XIAOYUsamaQAQ123/senior-design-notebook/notebook/Liangcheng Sun/final_presentation.pdf

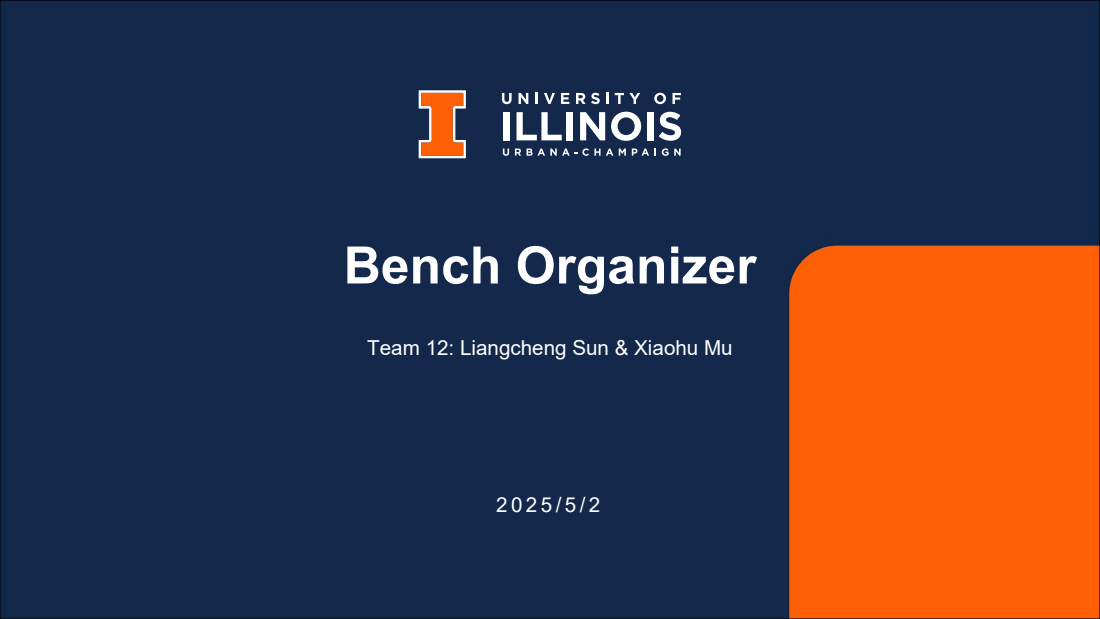
[picture p12: page 1]
Bench Organizer

Team 12: Liangcheng Sun & Xiaohu Mu

## Introduction

Our project aims to improve tool tracking and management in workspaces

We redesigned our original vision to simplify hardware and strengthen real-time alerting.

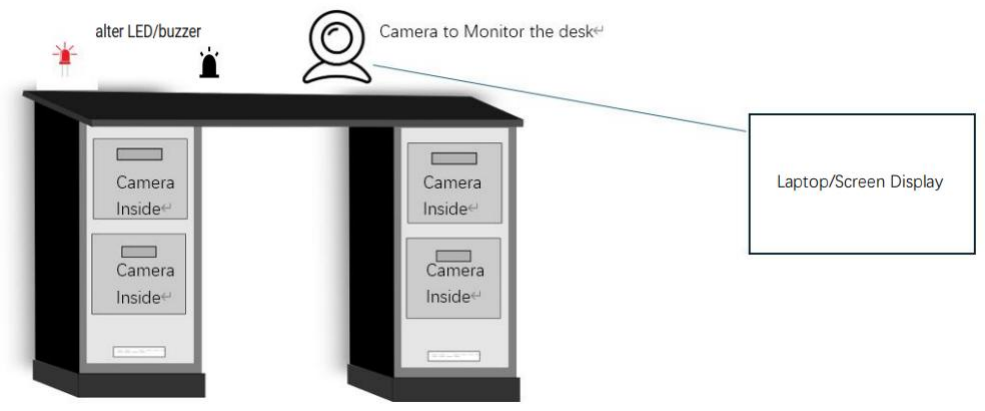
[picture p13: figure]

E L E C T R I C A L & C O M P U T E R E N G I N E E R I N G | G R A I N G E R E N G I N E E R I N G

## Objective

What problem are we solving?

- Tools are frequently misplaced or left out. • Manual systems like sign-out sheets are unreliable. Our goal: build a camera-based, automated tool detection and alert system.

## High-Level Requirements

1. Accuracy and Responsiveness

System should recognize ≥ 90% of tools using YOLO

Recognition time < 2 seconds

2. Robustness

Works reliably under different lighting

Can distinguish “place” vs “remove” actions

3. Extended Functionality

Alerts user on unknown tools

Allows learning new tool categories (custom labeling)

## Project Design

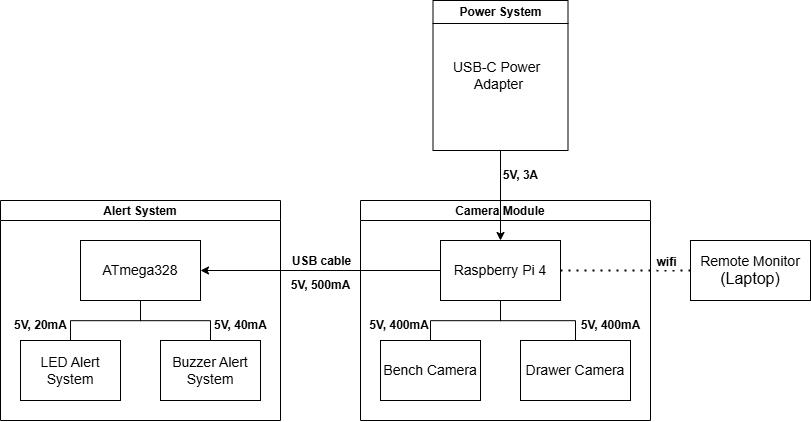
[picture p14: figure]

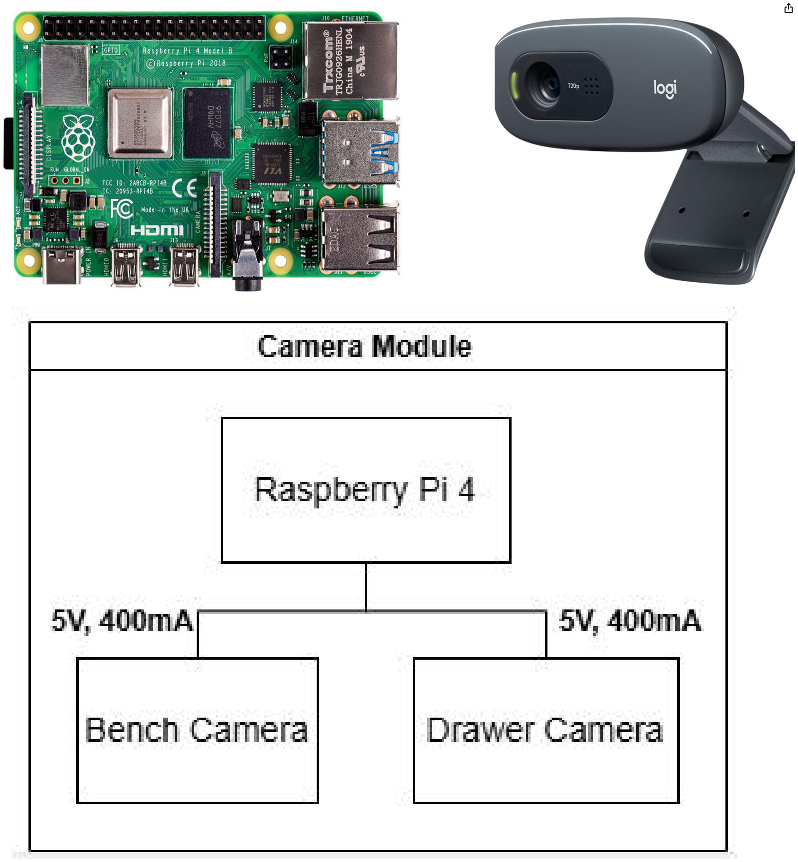
[picture p15: figure]

## Image Detection (Raspberry Pi)

Description:

- Use YOLO-based model to detect tools on bench and in drawer. • Use two webcams connected to Raspberry Pi. • Run detection every 10 seconds and check tool status. Requirements:
- Detect and classify all tools in the scene. • Differentiate between present, added, and missing tools. • Track missing tools for over 30 seconds.

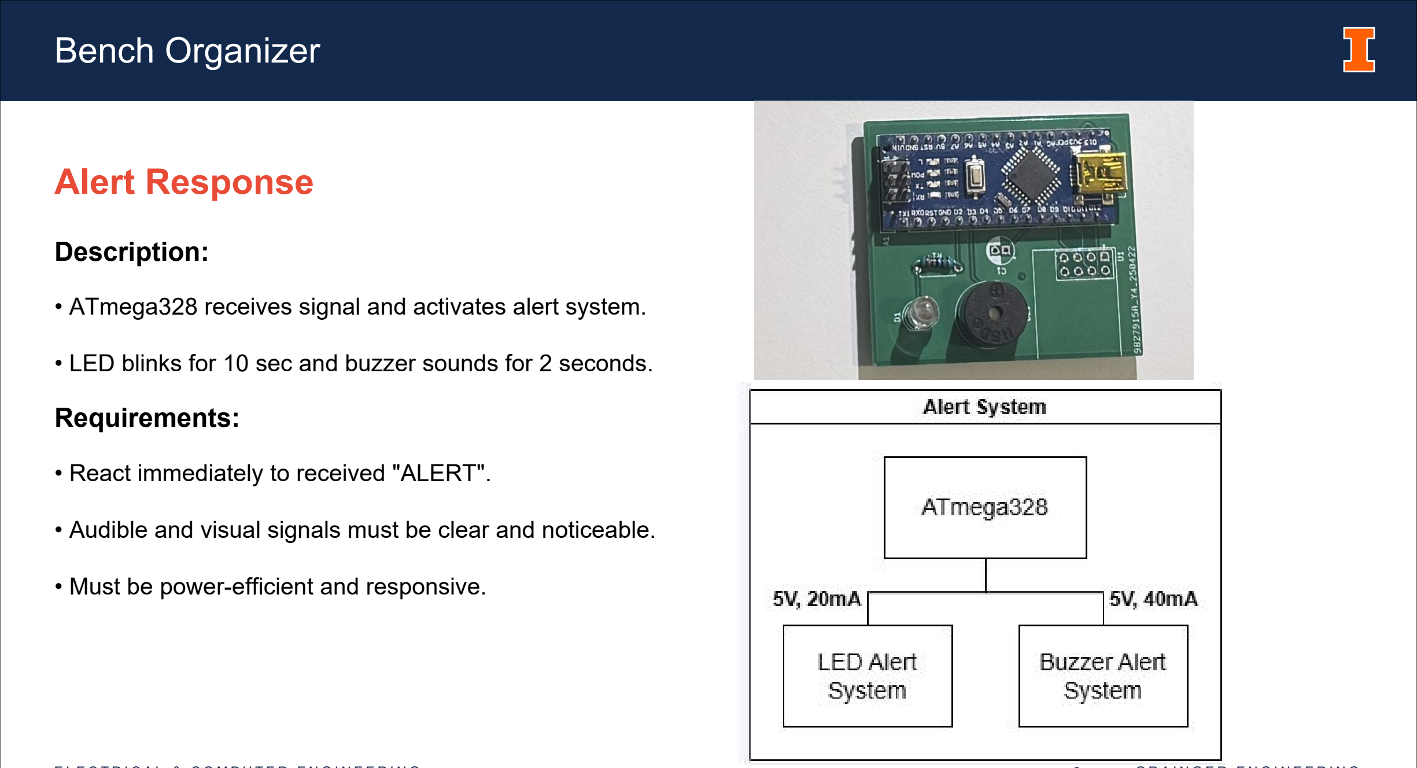
[picture p16: figure]
Alert Response; Bench Organizer; Description:

- ATmega328 receives signal and activates alert system. • LED blinks for 10 sec and buzzer sounds for 2 seconds. Requirements:
- React immediately to received "ALERT". • Audible and visual signals must be clear and noticeable. • Must be power-efficient and responsive.

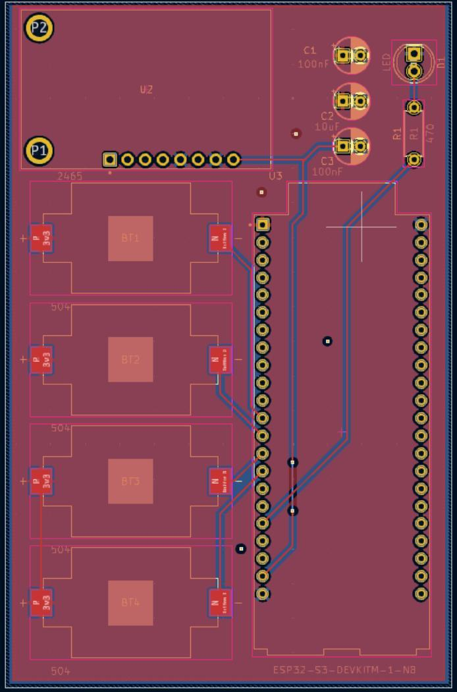
[picture p17: figure]
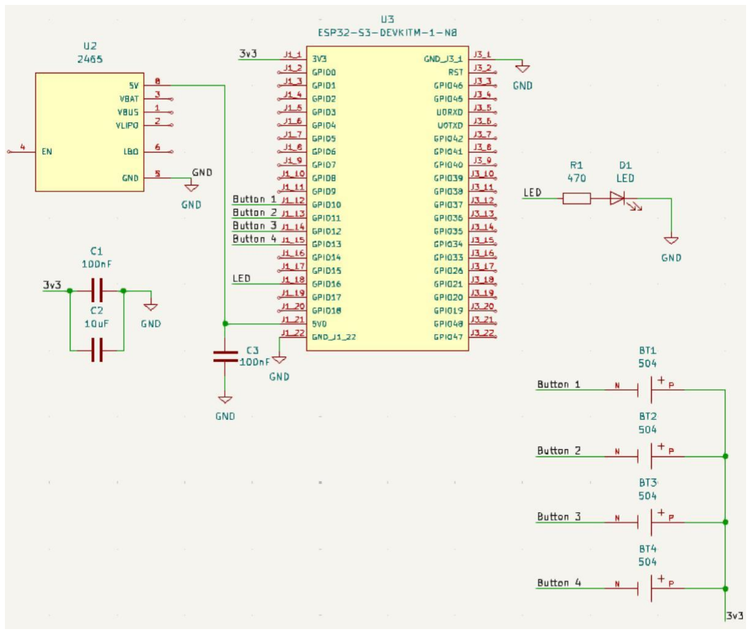
[picture p18: figure]

Original design(no longer used):

- ESP32
- Camera Module
- OLED screen

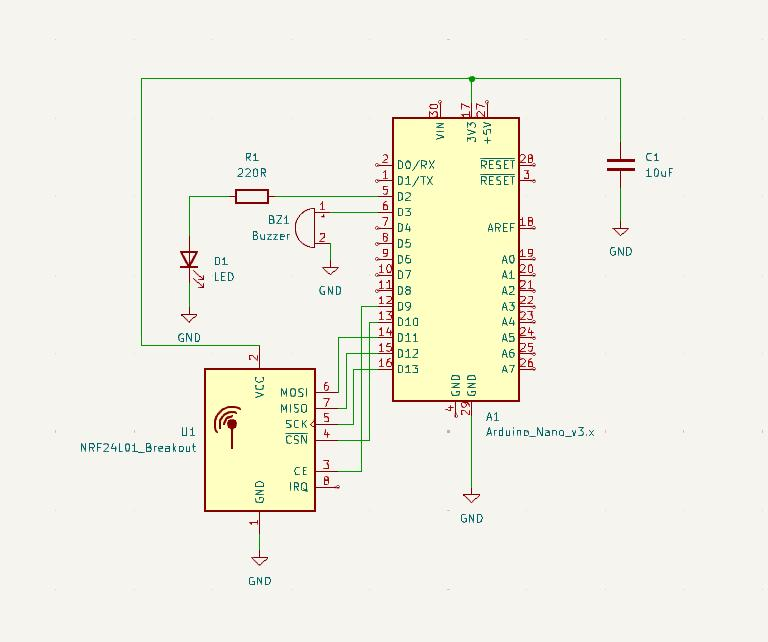
[picture p19: figure]
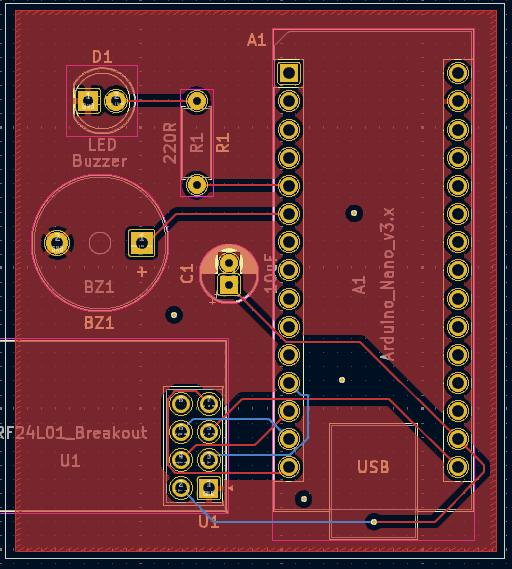
[picture p20: figure]

Final design:

- Raspberry Pi 4 with YOLOv5 object detection
- Two webcams: one for bench, one for drawer
- ATmega328 + LED + buzzer for alerts
- Fully remote control via laptop

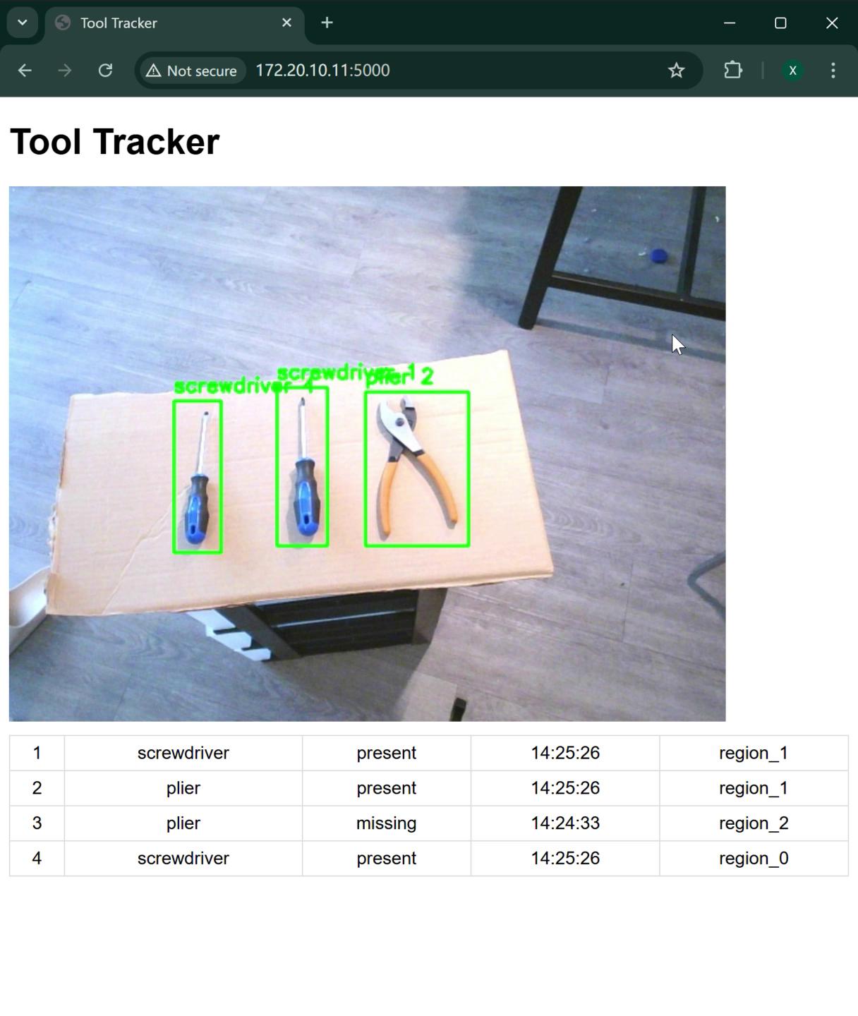
[picture p21: figure]

## Project Build & Test

- Python + YOLOv5 on Raspberry Pi detects tools every 10s
- Tool info (present/missing) shown on laptop UI
- If a tool is missing for over 30 seconds:
→ Raspberry Pi sends signal to ATmega328
→ ATmega328 receives and activates LED & buzzer
- Demo includes live webcam feed from Pi + alerts on missing tools

## Model Accuracy

Test Environment | Precision | Recall | Accuracy
Bench Tools (Camera 1) | 92% | 88% | 90%
Drawer Tools (Camera 2) | 89% | 85% | 87%
Combined | 90.5% | 86.5% | 88.5%

## Successes & Challenges

Success:

- Accuracy & Responsiveness: • Detection accuracy ~90% for trained tools
- Each detection completes within ~1.5 sec
- Alert Mechanism: • LED + buzzer alert triggers correctly when tool is missing for > 30s

## Successes & Challenges

Not Fully Met:

- Extended Functionality: • No real-time learning of unknown tools
- User labeling not yet implemented
- Current system only tracks pre-trained tool classes
- System cannot functions well under different lighting

## Conclusions

- We successfully implemented a YOLO-based system to detect missing tools in real time
- Communication with ATmega328 enables effective visual & sound alerts
- Dual-camera setup enhances monitoring coverage

## What We Learned

- Hardware units are prone to failure(e.g. loose connections, poor soldering, unstable power)
- Order multiple units at once for backup and faster troubleshooting
- Early hardware and integration tests are crucial for system stability

## Future Work

- Train larger custom YOLO model for more tool types
- Add support for multiple drawers/cameras
- Add persistent tool tracking with timestamps
- Deploy system in real lab setting

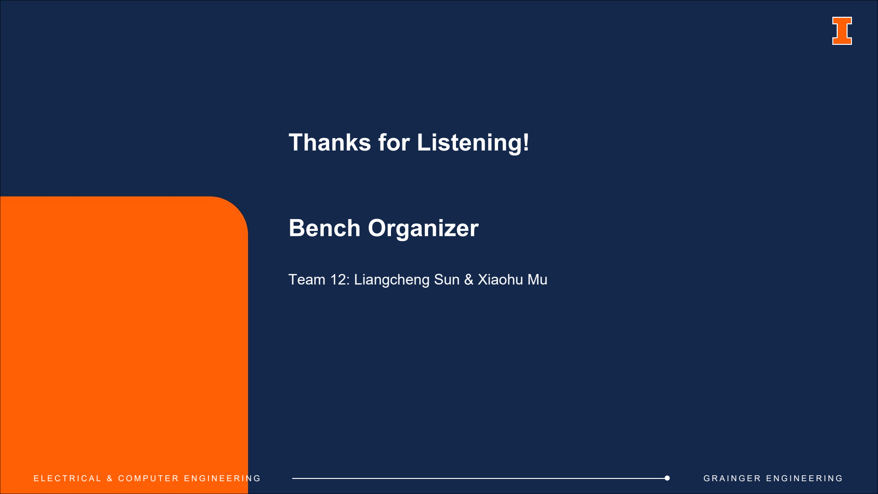
[picture p22: page 16]

## Thanks for Listening!

## Bench Organizer

Team 12: Liangcheng Sun & Xiaohu Mu

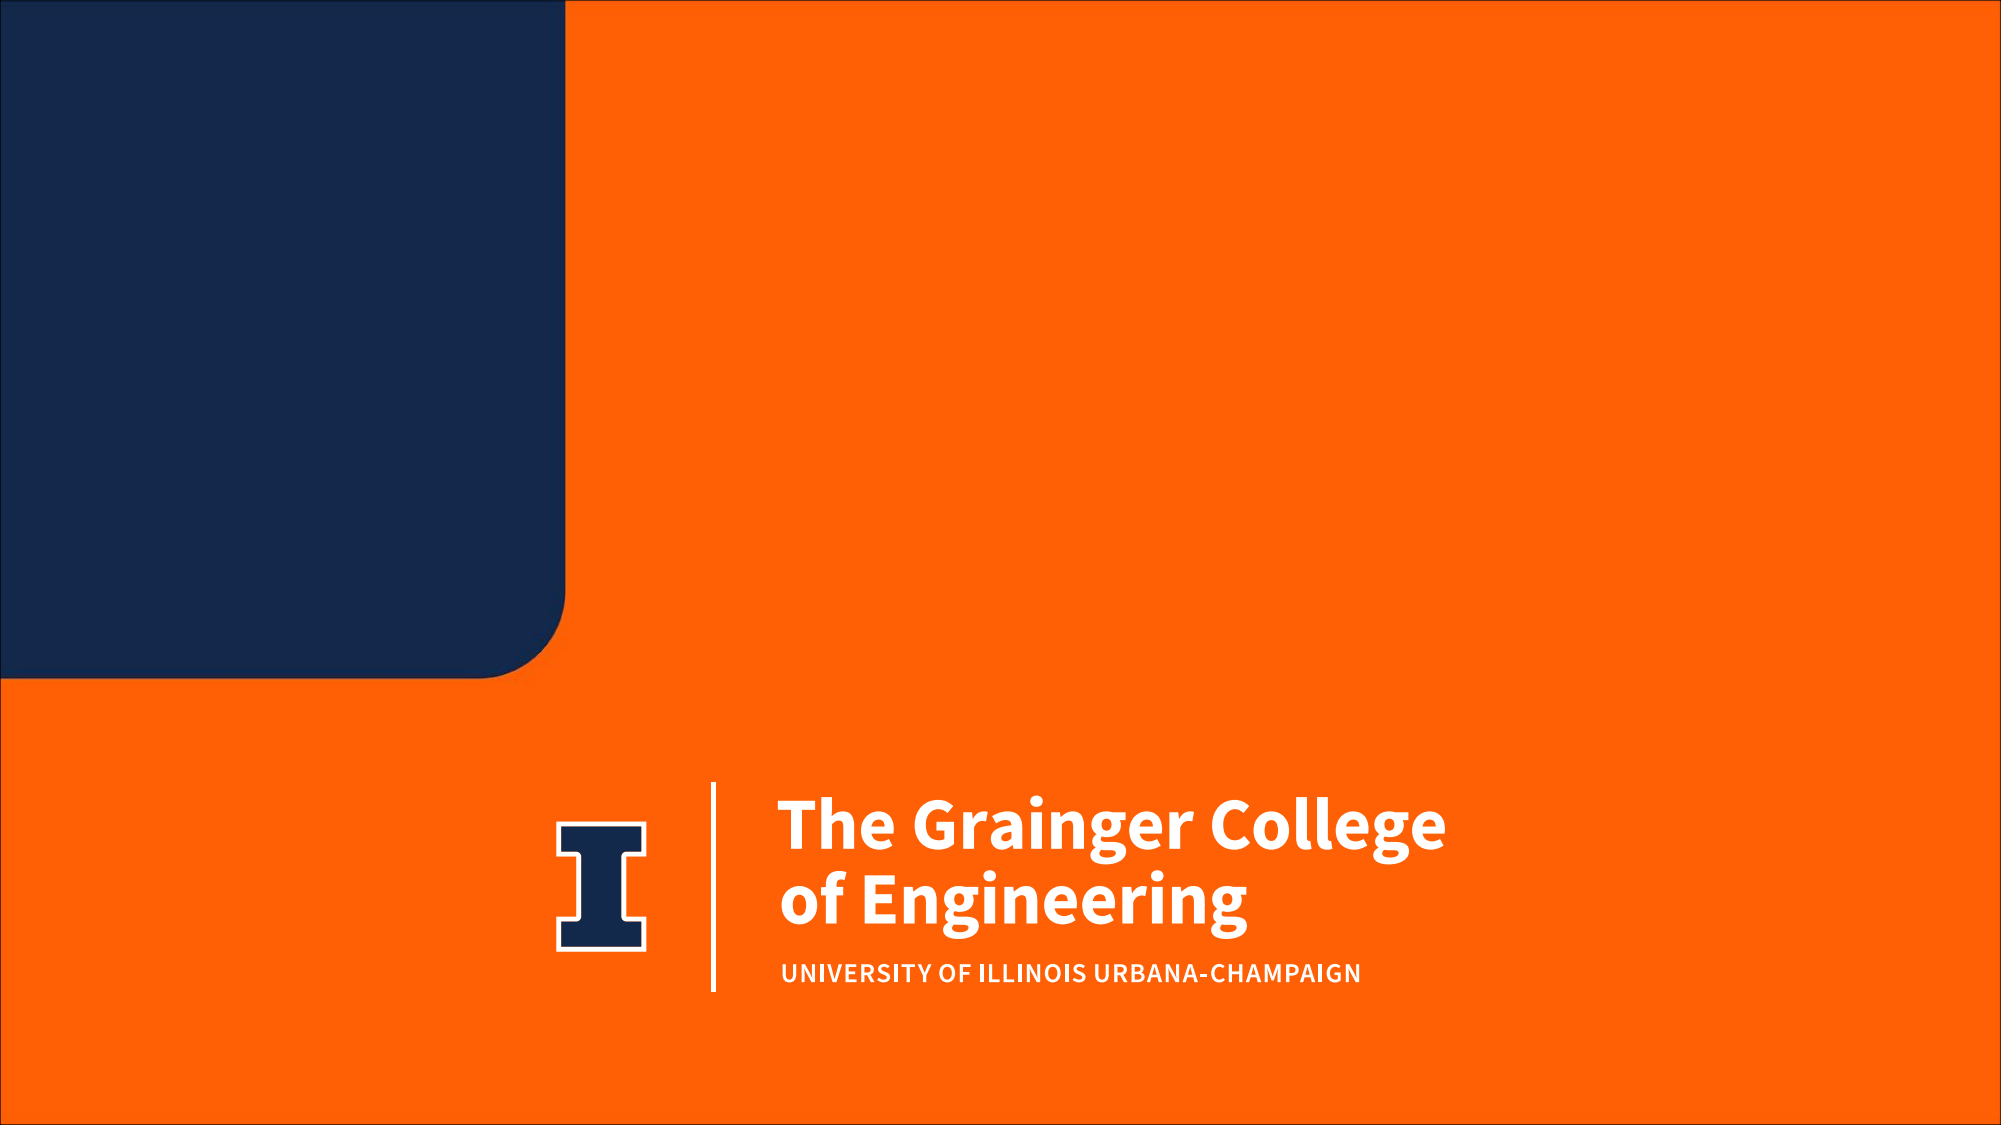
[picture p23: page 17]
