XIAOYUsamaQAQ123/senior-design-notebook/notebook/Liangcheng Sun/final_block_diagram.pdf

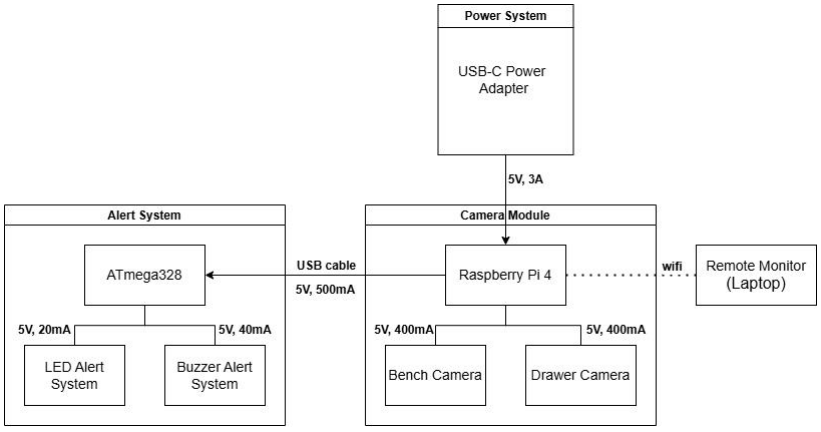
[picture p31: figure]
