XIAOYUsamaQAQ123/senior-design-notebook/experiment/yolo_detection_testing/autodetect_results_2025-04-17/images/img_6.jpg

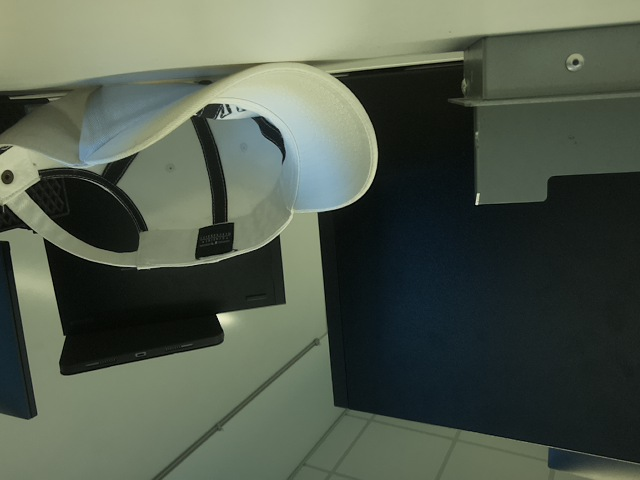
experiment/yolo_detection_testing/autodetect_results_2025-04-17/images/img_6.jpg
