XIAOYUsamaQAQ123/senior-design-notebook/experiment/yolo_detection_testing/autodetect_results_2025-04-17/result_2/img_2.jpg

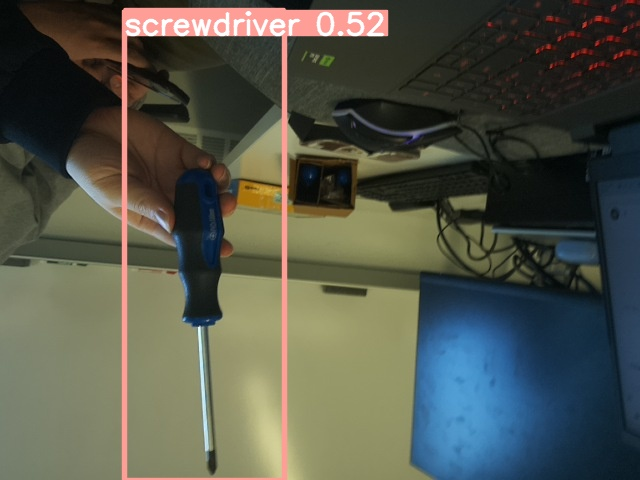
experiment/yolo_detection_testing/autodetect_results_2025-04-17/result_2/img_2.jpg
