XIAOYUsamaQAQ123/senior-design-notebook/notebook/Liangcheng Sun/test_image_result/autodetect_results_2025_04_15/detect/exp5/frame_20250415_195414.jpg

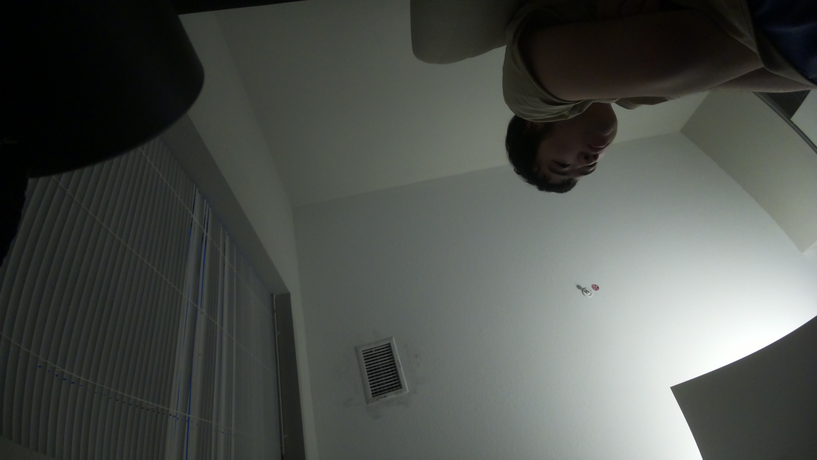
notebook/Liangcheng Sun/test_image_result/autodetect_results_2025_04_15/detect/exp5/frame_20250415_195414.jpg
